Alwinn07/Power-Distribution-Board-using-CCG30-48-05S-IC/Images/Back Copper.png

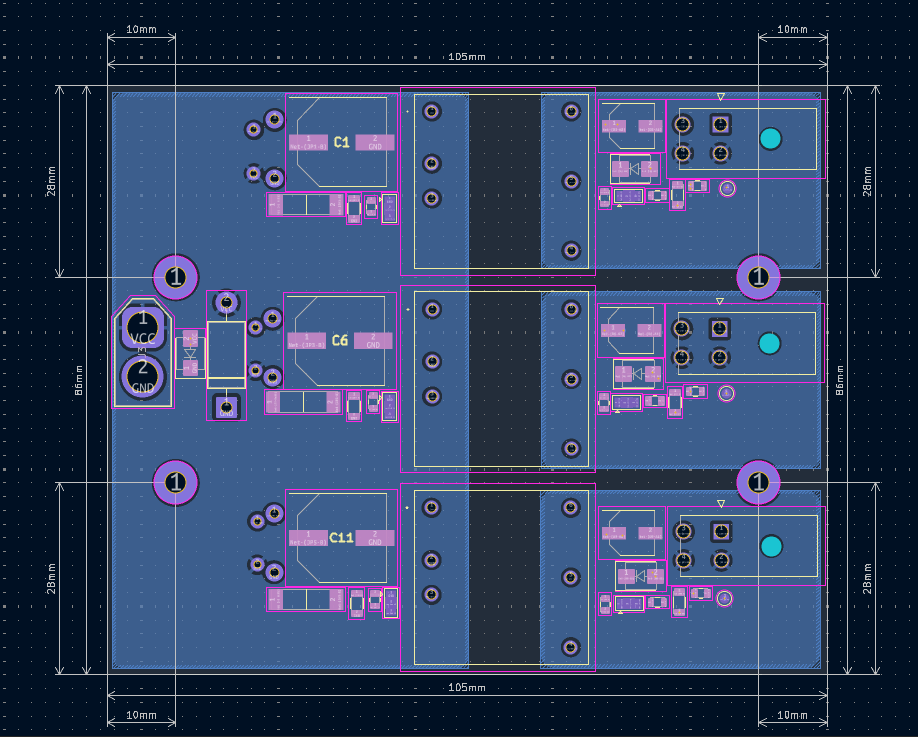
Images/Back Copper.png
